toml0006/gridfinity-spool-holder/renders/spool_detail.png

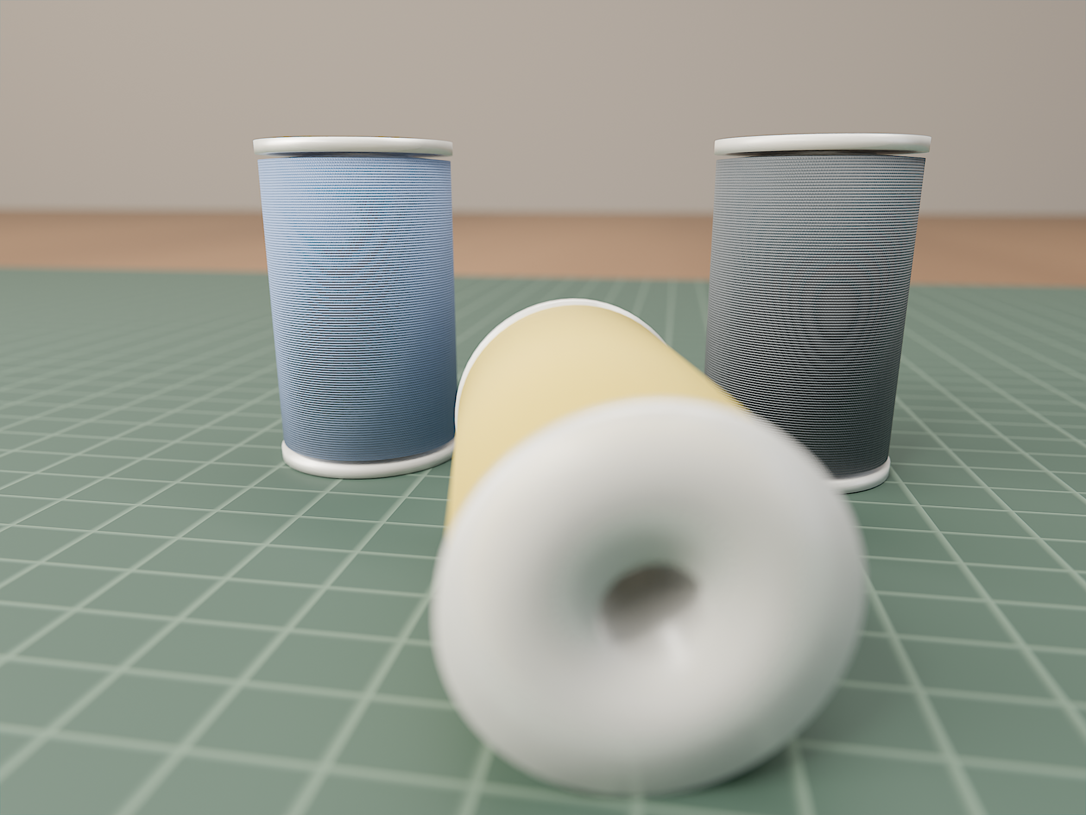
renders/spool_detail.png
