toml0006/gridfinity-spool-holder/renders/stacked.png

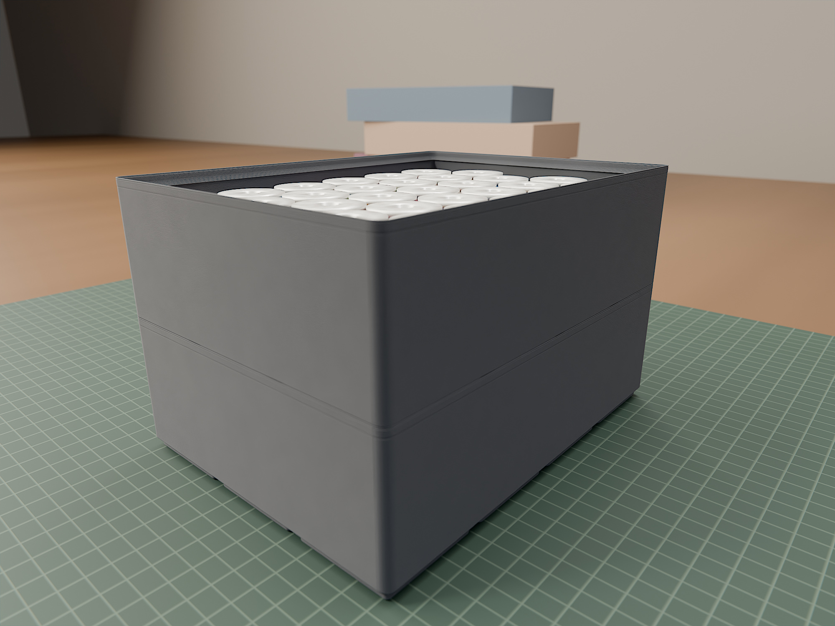
renders/stacked.png
